stephenhouser/Overnight-Sensations/subwoofer-turtle2/Turtle-diagram.jpg

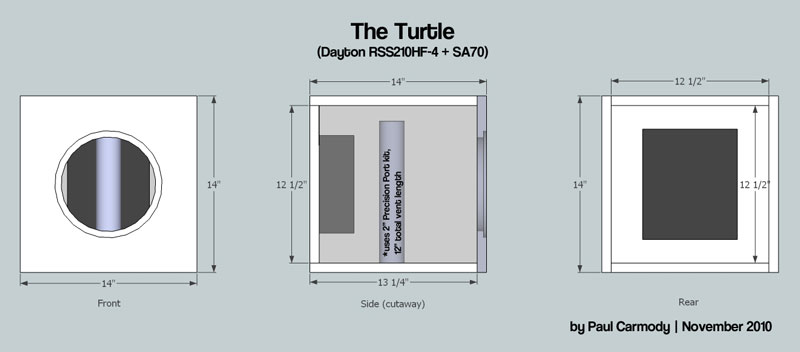
subwoofer-turtle2/Turtle-diagram.jpg
